retromuz/atmega328p-powerwall/photos/powerwall-web-ui-charging-on-a-heavily-cloudy-day.png

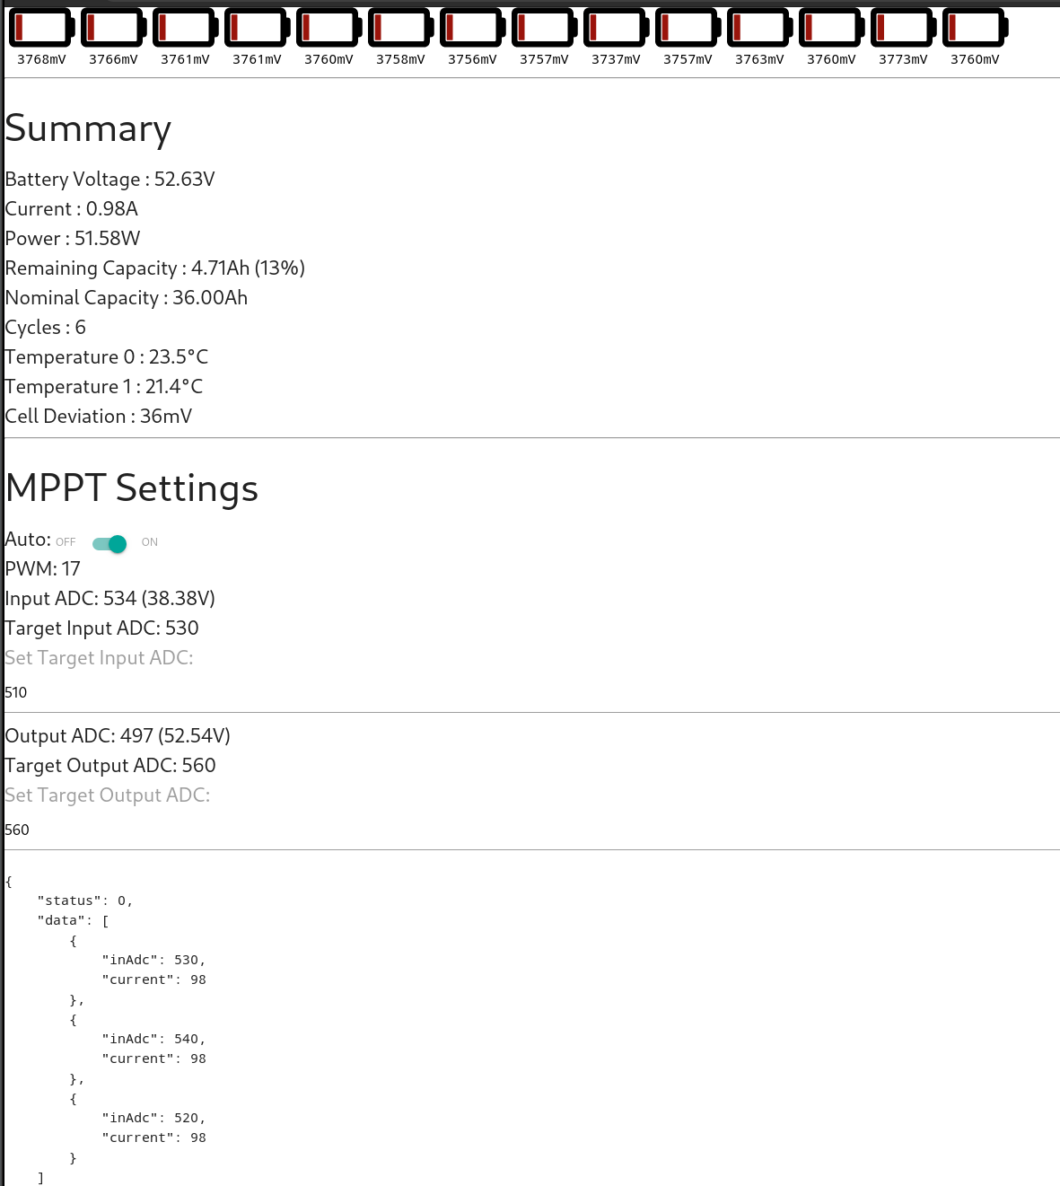
photos/powerwall-web-ui-charging-on-a-heavily-cloudy-day.png
